Cookie150CC/TempPi/Source/tests.py

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
import TSensor
import Messenger
import Config
import unittest

class TestTSensor(unittest.TestCase):

    def test_get_temp(self):#test for regular use case when correct sensor is provided
        
        tSensorObj = TSensor.TSensor()
        t0,h0 = tSensorObj.getTemp(0)
        t1,h1 = tSensorObj.getTemp(1)
        #print('Temp={0:0.1f}*F\n'.format(h))
        self.assertIsNotNone(t0, "Error with temp reading from TSensor 0. None returned as temp")
        self.assertIsNotNone(t1, "Error with temp reading from TSensor 1. None returned as temp")
        self.assertIsNotNone(h0, "Error with humidity reading from TSensor 0. None returned as humidity")
        self.assertIsNotNone(h1, "Error with humidity reading from TSensor 1. None returned as humidity")

    def test_get_avg_temp(self):#test for regular use cases

        tSensorObj = TSensor.TSensor()
        tAvg,hAvg = tSensorObj.getAvgTemp()
        self.assertIsNotNone(tAvg, "Error with temp reading from a sensor. None returned as Avg Temp")

class TestMessenger(unittest.TestCase):
    
    def test_send_msg(self):
        configObj = Config.Config()
        configObj.openJSON()
        messengerObj = Messenger.Messenger()
        tSensorObj = TSensor.TSensor()
        tAvg,hAvg = tSensorObj.getAvgTemp()
        retval = messengerObj.sendMsg(configObj,tAvg)
        self.assertEquals(retval,0,'Error sending message from sendMsg()')

if __name__ == '__main__':
        unittest.main()
